MarcoBraun84/PongGame-ESP32-VGA/PONG ESP32 Schaltplan.kicad_sch

## KiCad design PONG ESP32 Schaltplan.kicad_sch (2024-03-17)

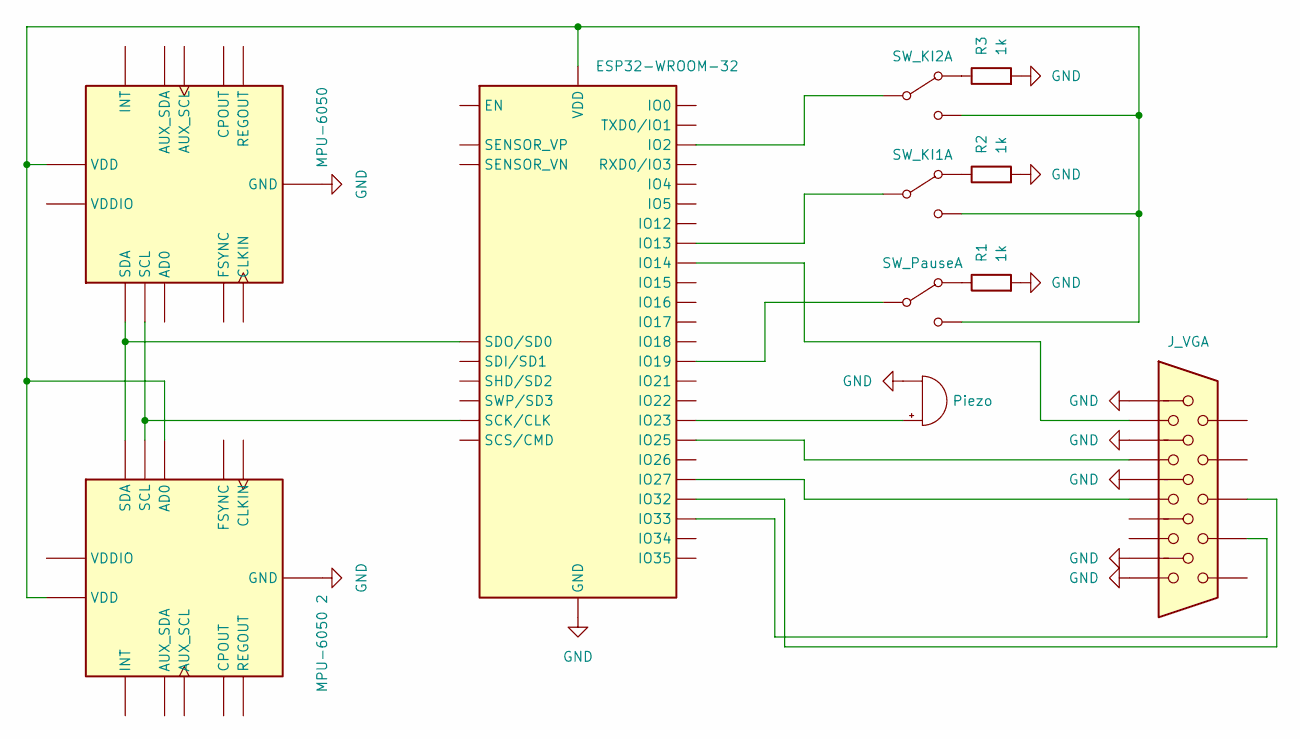
[picture p2: schematic PONG ESP32 Schaltplan.kicad_sch]

Parts:
J_VGA: DB15_Female_HighDensity
R1, R2, R3: 1k
SW_KI1, SW_KI2: SW_DPDT_x2
SW_Pause: SW_DPDT_x2

Connections:
GND: J_VGA.5, J_VGA.6, J_VGA.7, J_VGA.8, R1.2, R2.2
unnamed: R1.1, SW_Pause.1 (A)
unnamed: R2.1, SW_KI1.1 (A)
unnamed: R3.1, SW_KI2.1 (A)
unnamed: SW_KI1.3 (C), SW_KI2.3 (C), SW_Pause.3 (C)
